ocelot47/delta-robot/image/filein3d_STL/12xpan_head_tapping_screw_am-39PHT_4x13x11_6-slot-D-S.stl

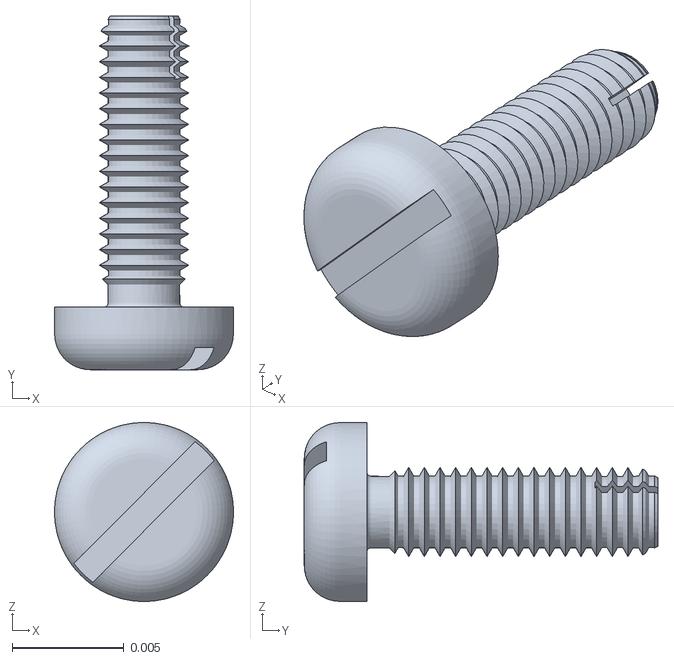
[picture p19: CAD file, 2026-04-28]
image/filein3d_STL/12xpan_head_tapping_screw_am-39PHT_4x13x11_6-slot-D-S.stl
0.008 x 0.0158 x 0.008
