ocelot47/delta-robot/image/filein3d_STL/12xpan_head_tapping_screw_am-28PHT_5x13x12_2-slot-D-S.stl

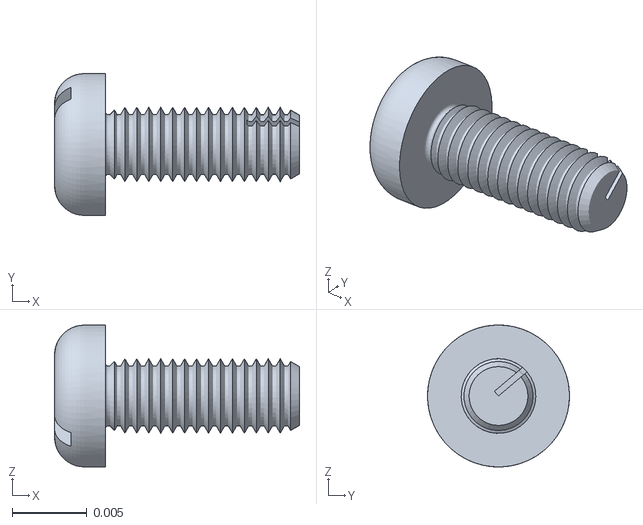
[picture p20: CAD file, 2026-04-28]
image/filein3d_STL/12xpan_head_tapping_screw_am-28PHT_5x13x12_2-slot-D-S.stl
0.0164 x 0.00949 x 0.00949
